adonutartist/Nemos-Hackpad-DONUT-PAD/assets/PCB kicad.jpg

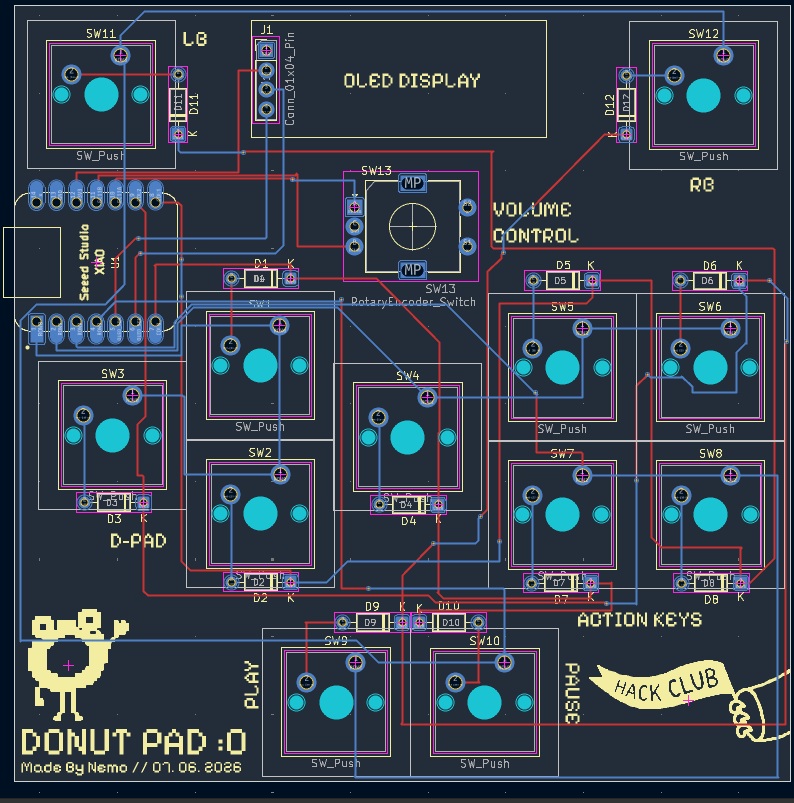
assets/PCB kicad.jpg
