adonutartist/Nemos-Hackpad-DONUT-PAD/assets/cad model exploded view.jpg

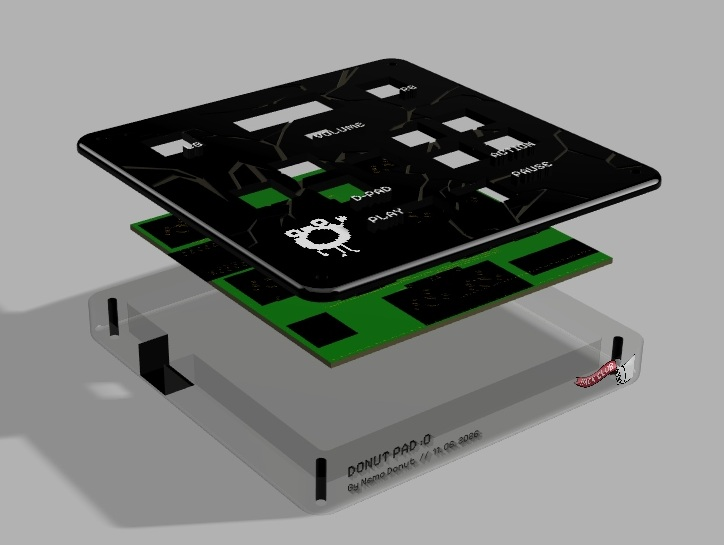
assets/cad model exploded view.jpg
